SDG2805/AQM-Smarthome/SchematicsOrWiringDiagramm/AQM_Blueprint.kicad_sch

## KiCad design SchematicsOrWiringDiagramm/AQM_Blueprint.kicad_sch (2026-01-07)

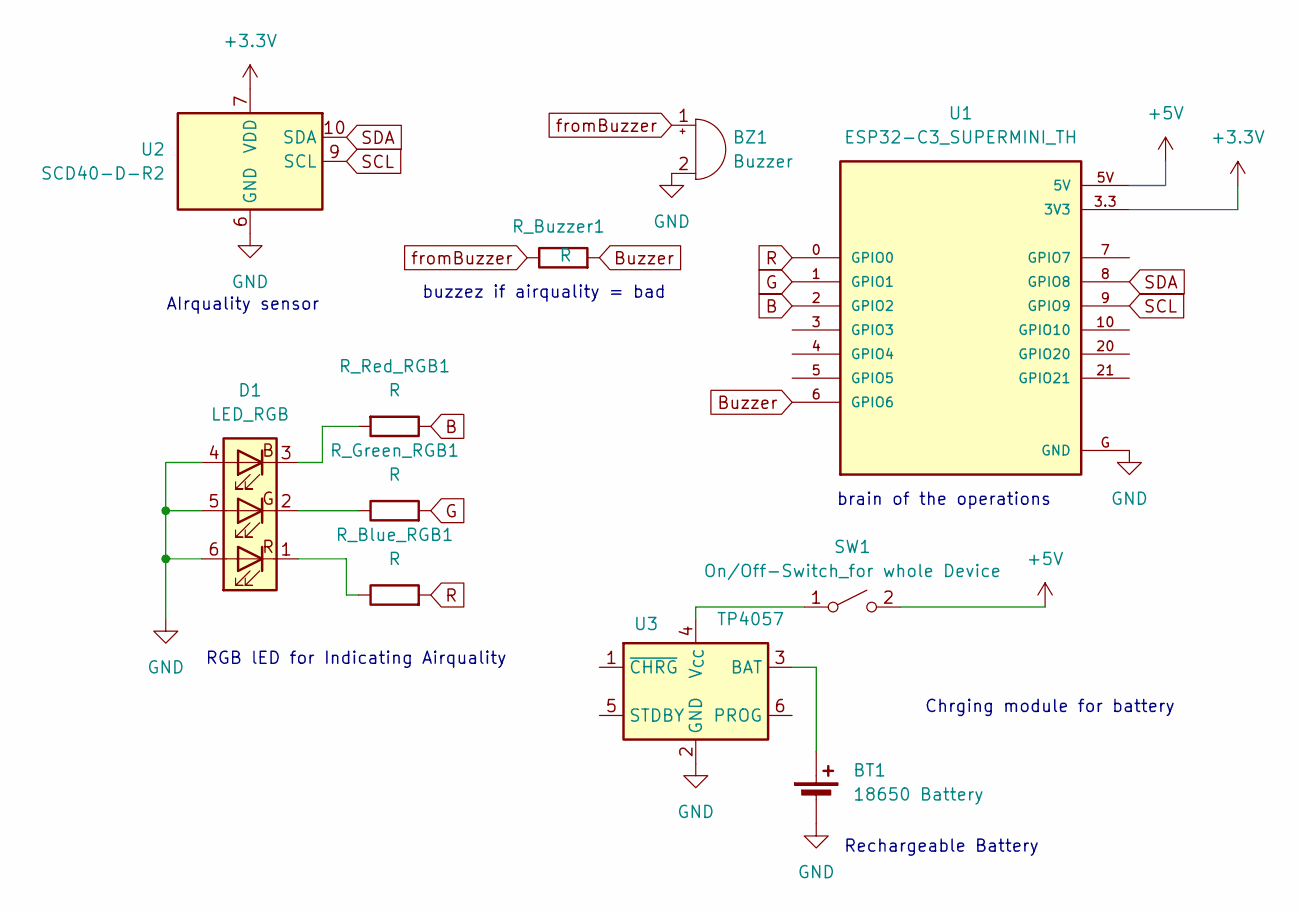
[picture p2: schematic AQM_Blueprint.kicad_sch]

Parts:
BT1: 18650 Battery
BZ1: Buzzer; CUI_CMI-9605IC-0380T
D1: LED_RGB; LED_D5.0mm-4_RGB
R_Blue_RGB1: R; R_0805_2012Metric_Pad1.20x1.40mm_HandSolder
R_Buzzer1: R; R_0805_2012Metric_Pad1.20x1.40mm_HandSolder
R_Green_RGB1: R; R_0805_2012Metric_Pad1.20x1.40mm_HandSolder
R_Red_RGB1: R; R_0805_2012Metric_Pad1.20x1.40mm_HandSolder
SW1: On/Off-Switch_for whole Device
U1: ESP32-C3_SUPERMINI_TH; MODULE_ESP32-C3_SUPERMINI_TH
U2: SCD40-D-R2; Sensirion_SCD4x-1EP_10.1x10.1mm_P1.25mm_EP4.8x4.8mm
U3: TP4057; TSOT-23-6

Connections:
+3.3V: U1.3.3 (3V3), U2.7 (VDD), U2.19 (VDD)
+5V: SW1.2 (B), U1.5V
B: R_Red_RGB1.1, U1.2 (GPIO2)
Buzzer: R_Buzzer1.2, U1.6 (GPIO6)
G: R_Green_RGB1.2, U1.1 (GPIO1)
GND: BT1.2 (-), BZ1.2 (-), D1.4 (BA), D1.5 (GA), D1.6 (RA), U1.G (GND), U2.6 (GND), U2.20 (GND), U2.21 (GND), U3.2 (GND)
unnamed: BT1.1 (+), U3.3 (BAT)
unnamed: D1.1 (RK), R_Blue_RGB1.1
unnamed: D1.2 (GK), R_Green_RGB1.1
unnamed: D1.3 (BK), R_Red_RGB1.2
unnamed: SW1.1 (A), U3.4 (V_{CC})
R: R_Blue_RGB1.2, U1.0 (GPIO0)
SCL: U1.9 (GPIO9), U2.9 (SCL)
SDA: U1.8 (GPIO8), U2.10 (SDA)
fromBuzzer: BZ1.1 (+), R_Buzzer1.1

Notes on the sheet:
Rechargeable Battery
brain of the operations
Chrging module for battery
buzzez if airquality = bad
AIrquality sensor
RGB lED for Indicating Airquality
